bzeiss/xfm2-pcbs/ui-board/xfm2_xva1-ui/src/synth/xfm2_hw.h

#ifndef XFM2HW_H
#define XFM2HW_H

#include <Arduino.h>

class Xfm2Hw {
public:
  explicit Xfm2Hw(HardwareSerial *serial);
  ~Xfm2Hw();
  void updateXfm2SynthModel();
  int loadProgram(byte programNumber);
  int writeProgram(byte programNumber);
  void setParameter(int parameterNumber, byte value);
  byte getParameter(int parameterNumber);
  int activateFirstUnit();
  int activateSecondUnit();
  void initializeEeprom();
  int setFirstUnitMidiChannel(byte channelNumber);
  int setSecondUnitMidiChannel(byte channelNumber);
  int setLayerMode(bool enabled);
  void printLastCommandResult() const;
  char *readXva1Name();
  void dump();
private:
  HardwareSerial *serial;
  byte lastResult;
  byte readResultByte();
  int const maxParameters = 394;

  void serialDrain();
};

#endif
