bzeiss/xfm2-pcbs/ui-board/xfm2_xva1-ui/src/synth/xfm2_operator.cpp

#include "xfm2_operator.h"

// ---------------------------------------------------------------------------------------

Xfm2Operator::Xfm2Operator() = default;

// ---------------------------------------------------------------------------------------

Xfm2Operator::~Xfm2Operator() = default;

// ---------------------------------------------------------------------------------------

void Xfm2Operator::setSynthParameter(byte parameter) {

}

// ---------------------------------------------------------------------------------------

void Xfm2Operator::setOperatorId(byte operatorIdParam) {
    this->operatorId = operatorIdParam;
}
